Pooja-Jayakanth/Smart-Grain-Storage-and-Mushroom-Monitoring-System/docs/Checking before adding MOSFET.jpeg

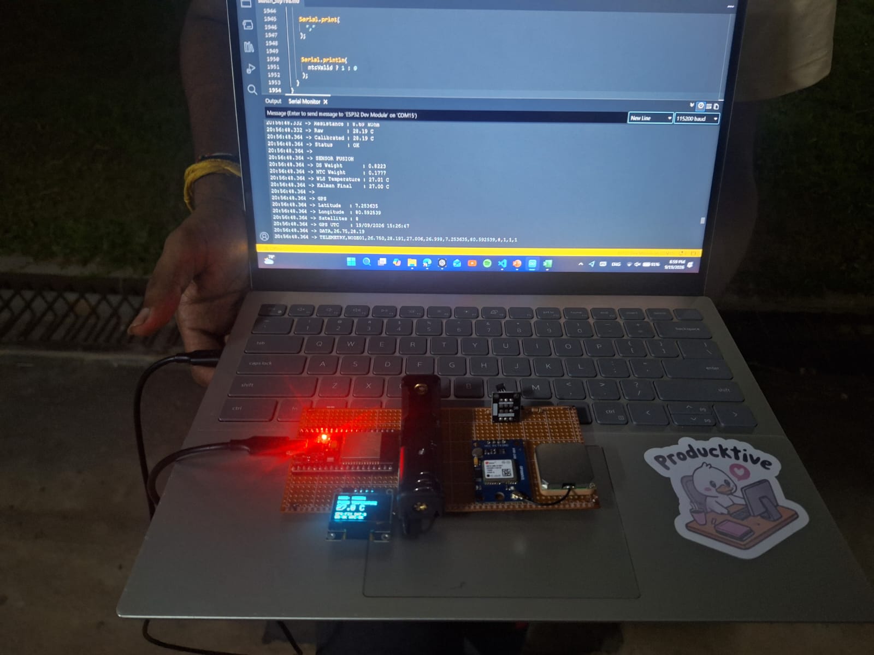
docs/Checking before adding MOSFET.jpeg
