Pooja-Jayakanth/Smart-Grain-Storage-and-Mushroom-Monitoring-System/docs/Checking MOSFET.jpeg

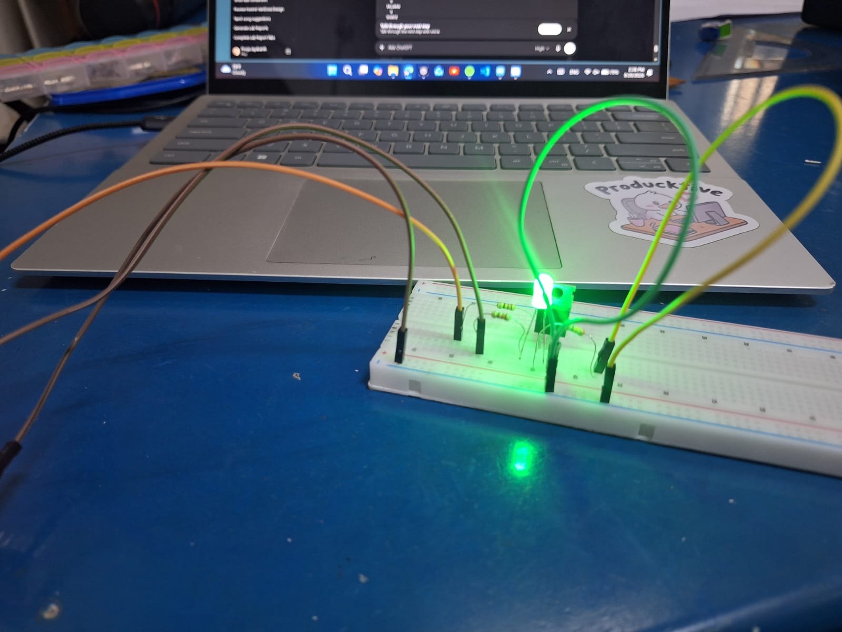
docs/Checking MOSFET.jpeg
