Pooja-Jayakanth/Smart-Grain-Storage-and-Mushroom-Monitoring-System/docs/Semifinal Prototype Node.jpeg

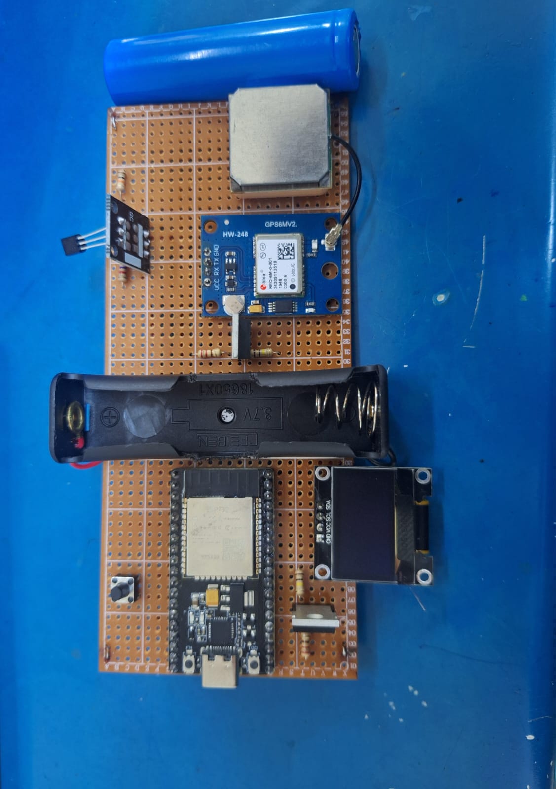
docs/Semifinal Prototype Node.jpeg
