Pooja-Jayakanth/Smart-Grain-Storage-and-Mushroom-Monitoring-System/hardware/mechanical/exploded view.PNG

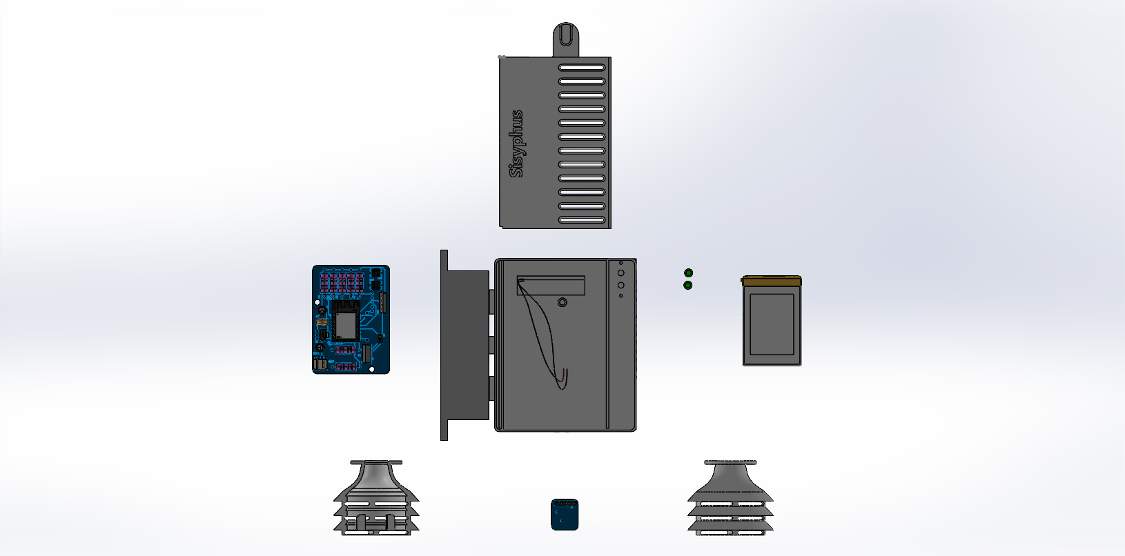
hardware/mechanical/exploded view.PNG
