Pooja-Jayakanth/Smart-Grain-Storage-and-Mushroom-Monitoring-System/hardware/pcb/sensor_holder_pcb/pcb_3d_view.png

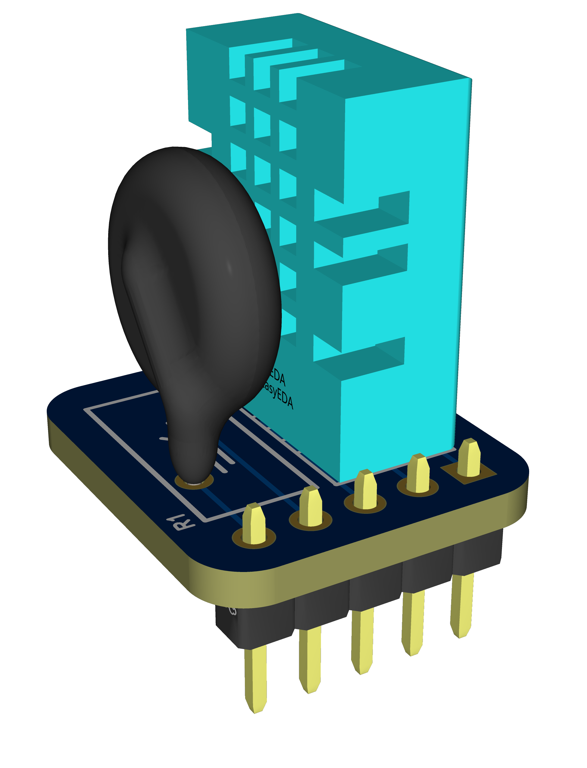
hardware/pcb/sensor_holder_pcb/pcb_3d_view.png
