Pooja-Jayakanth/Smart-Grain-Storage-and-Mushroom-Monitoring-System/hardware/schematic/Sensor_holder_Schematic.png

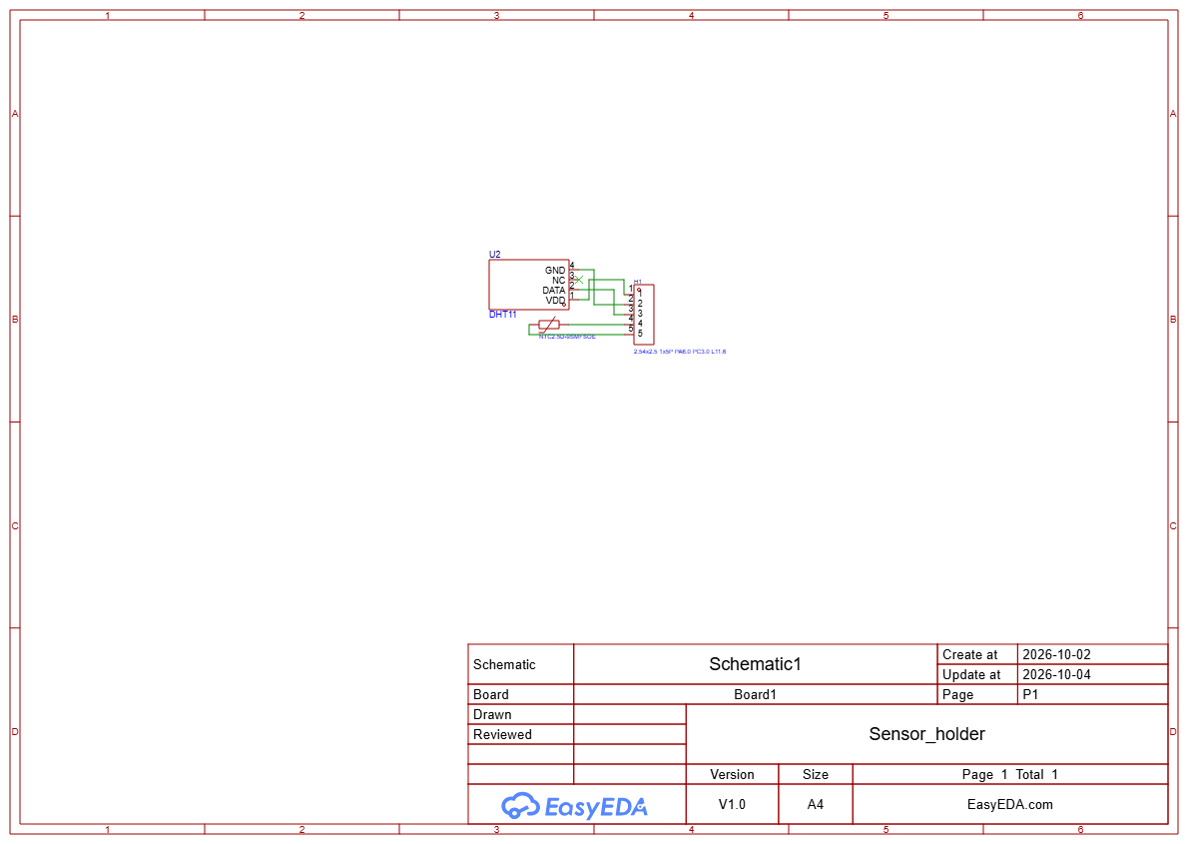
hardware/schematic/Sensor_holder_Schematic.png
