Pooja-Jayakanth/Smart-Grain-Storage-and-Mushroom-Monitoring-System/sensor-fusion-and-callibration/01_after_EMA_filtering.png

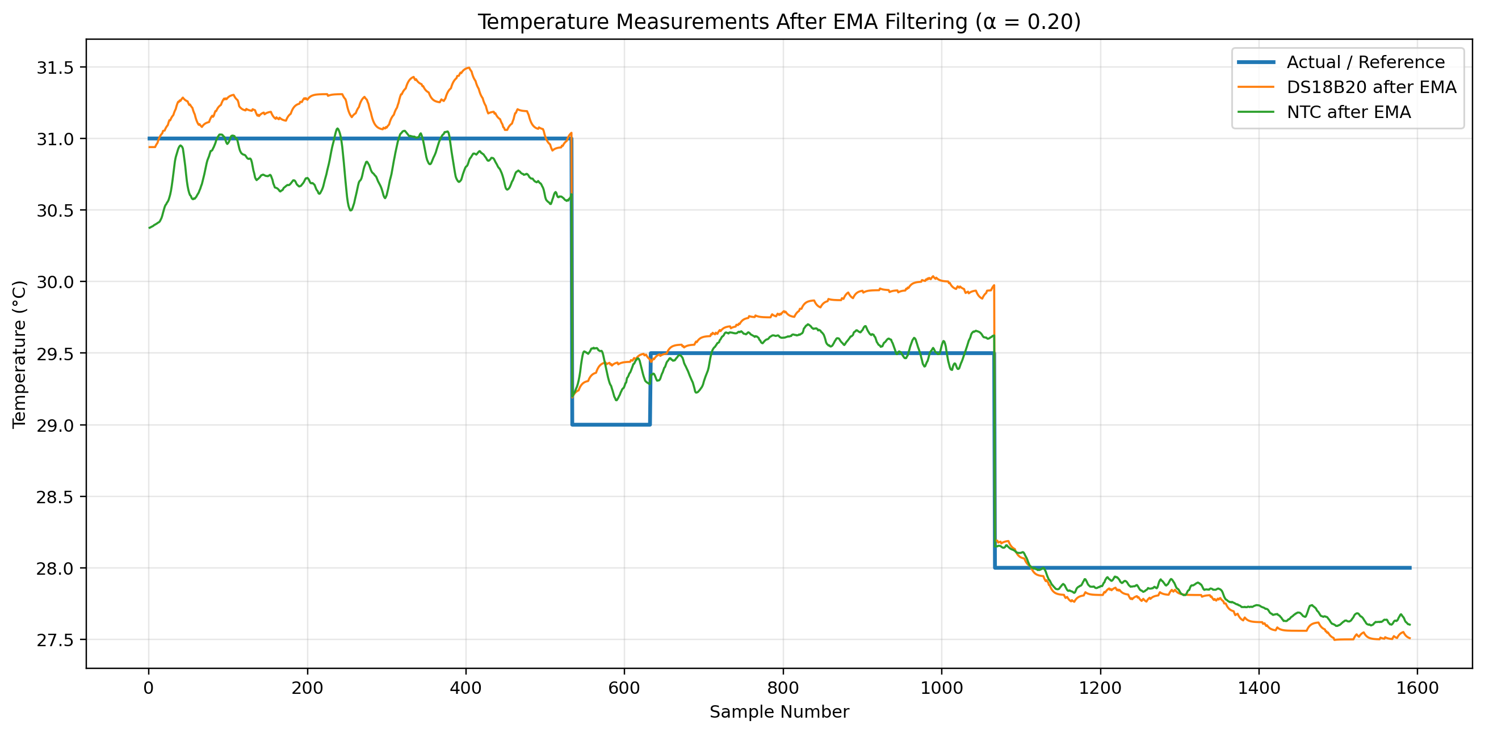
sensor-fusion-and-callibration/01_after_EMA_filtering.png
