Pooja-Jayakanth/Smart-Grain-Storage-and-Mushroom-Monitoring-System/sensor-fusion-and-callibration/03_after_WLS_and_Kalman.png

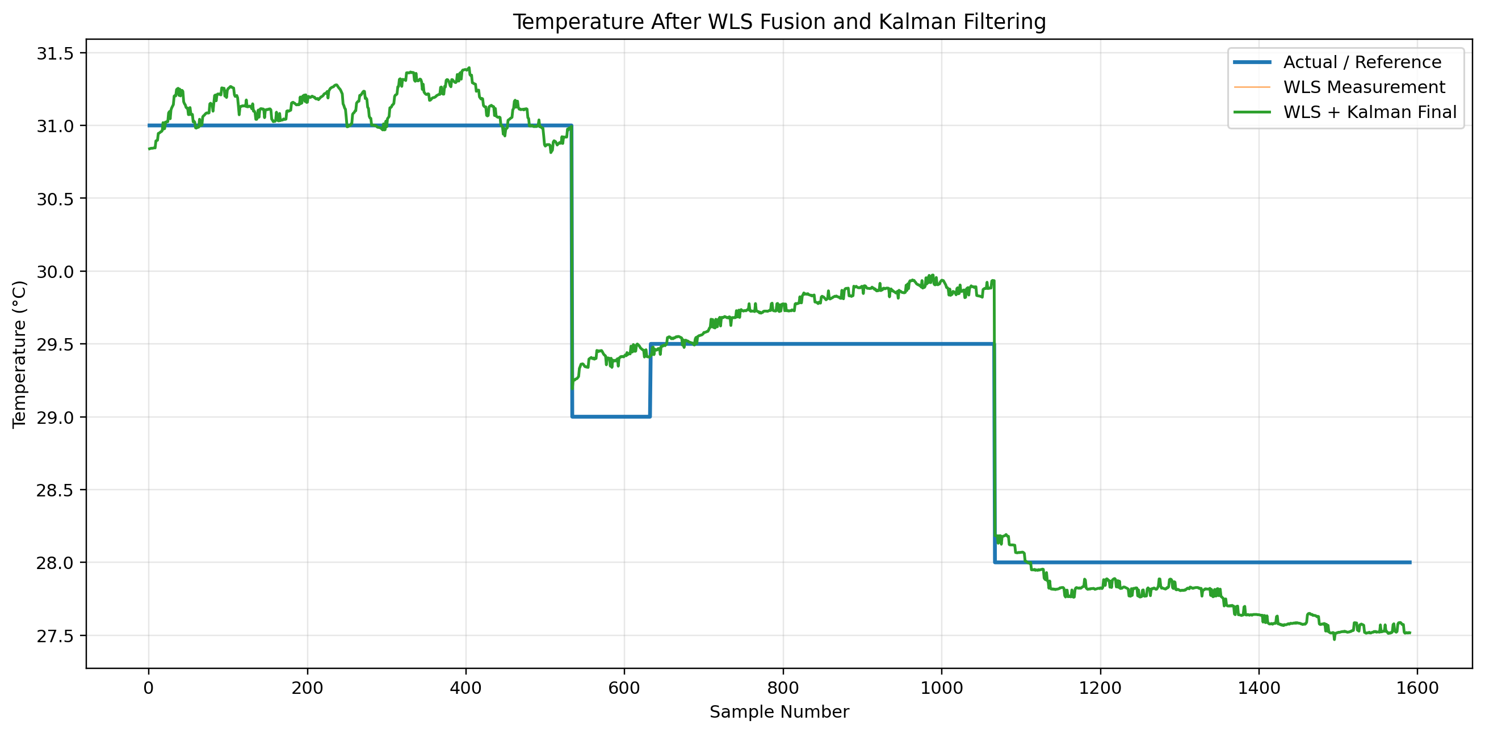
sensor-fusion-and-callibration/03_after_WLS_and_Kalman.png
