Pooja-Jayakanth/Smart-Grain-Storage-and-Mushroom-Monitoring-System/sensor-fusion-and-callibration/Raw vs EMA-Filtered Temperature Readings.jpeg

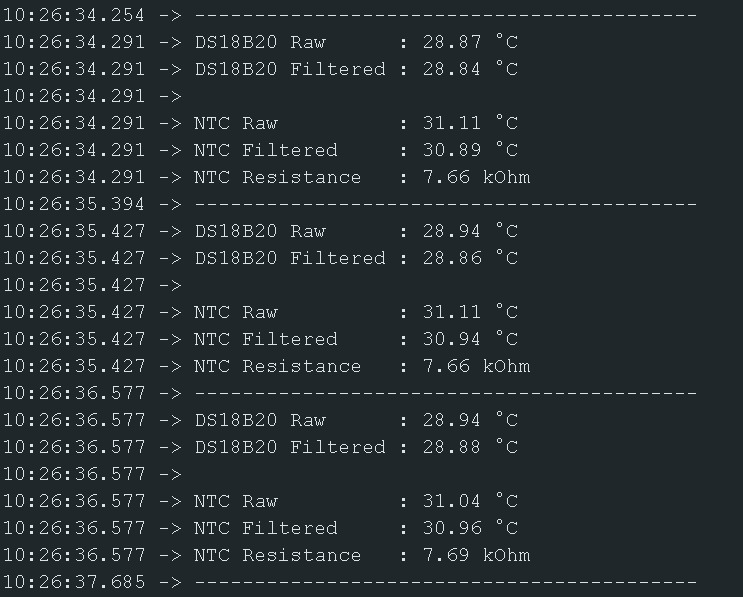
sensor-fusion-and-callibration/Raw vs EMA-Filtered Temperature Readings.jpeg
