Pooja-Jayakanth/Smart-Grain-Storage-and-Mushroom-Monitoring-System/sensor-fusion-and-callibration/Real-Time Sensor Fusion and Kalman Filter Output.jpeg

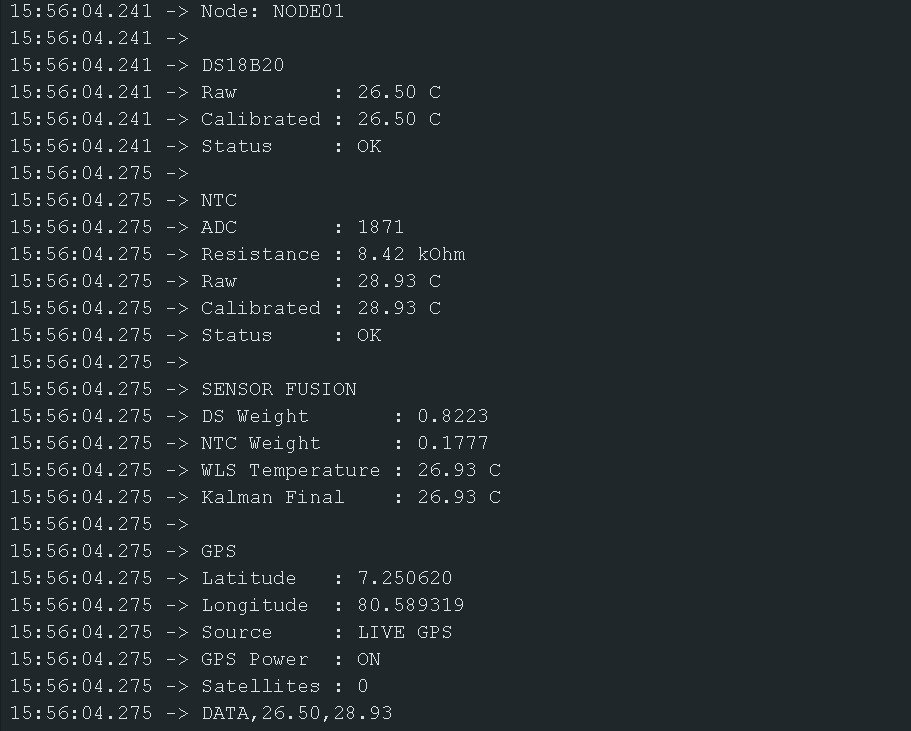
sensor-fusion-and-callibration/Real-Time Sensor Fusion and Kalman Filter Output.jpeg
