Pooja-Jayakanth/Smart-Grain-Storage-and-Mushroom-Monitoring-System/sensor-fusion-and-callibration/28 °C Sensor Calibration Results.jpeg

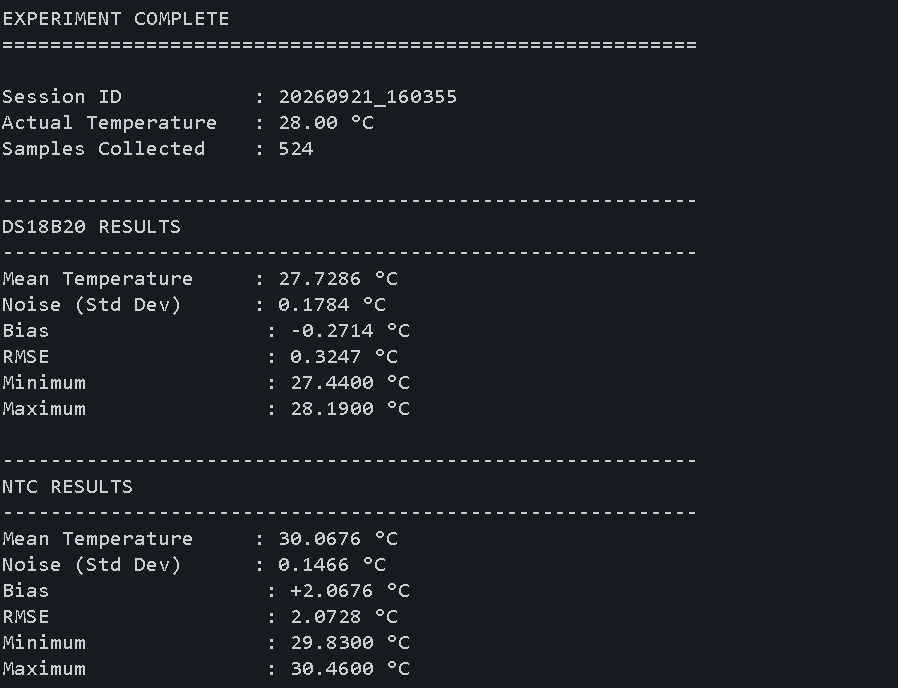
sensor-fusion-and-callibration/28 °C Sensor Calibration Results.jpeg
