Pooja-Jayakanth/Smart-Grain-Storage-and-Mushroom-Monitoring-System/sensor-fusion-and-callibration/Pre-Calibration Sensor Fusion Results.jpeg

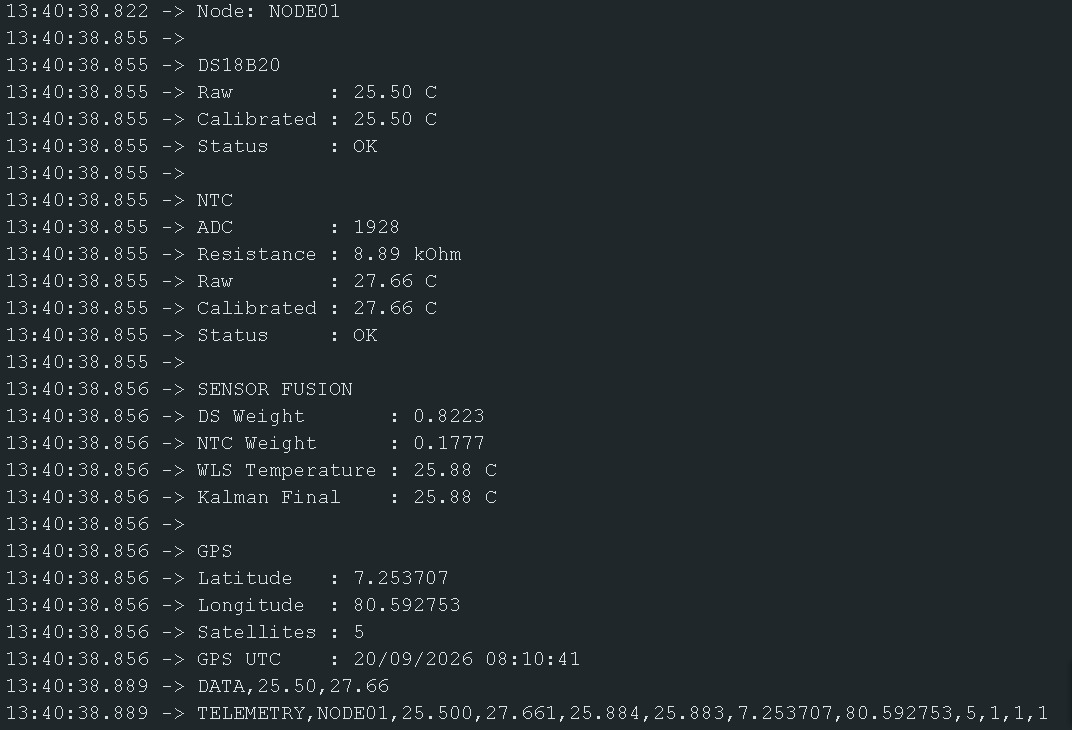
sensor-fusion-and-callibration/Pre-Calibration Sensor Fusion Results.jpeg
