Pooja-Jayakanth/Smart-Grain-Storage-and-Mushroom-Monitoring-System/sensor-fusion-and-callibration/Sensor Noise Characterization of DS18B20 and NTC Thermistor (100 Samples).jpeg

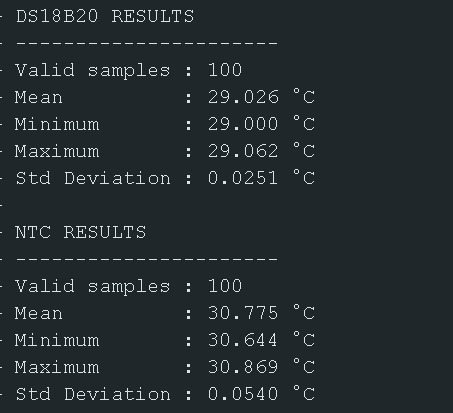
sensor-fusion-and-callibration/Sensor Noise Characterization of DS18B20 and NTC Thermistor (100 Samples).jpeg
